ManchesterStingerMotorsports/BSPD-2026/BSPD 1003/BSPD PCB/BSPD 1003.kicad_sch

## KiCad design BSPD 1003/BSPD PCB/BSPD 1003.kicad_sch (2026-02-10)

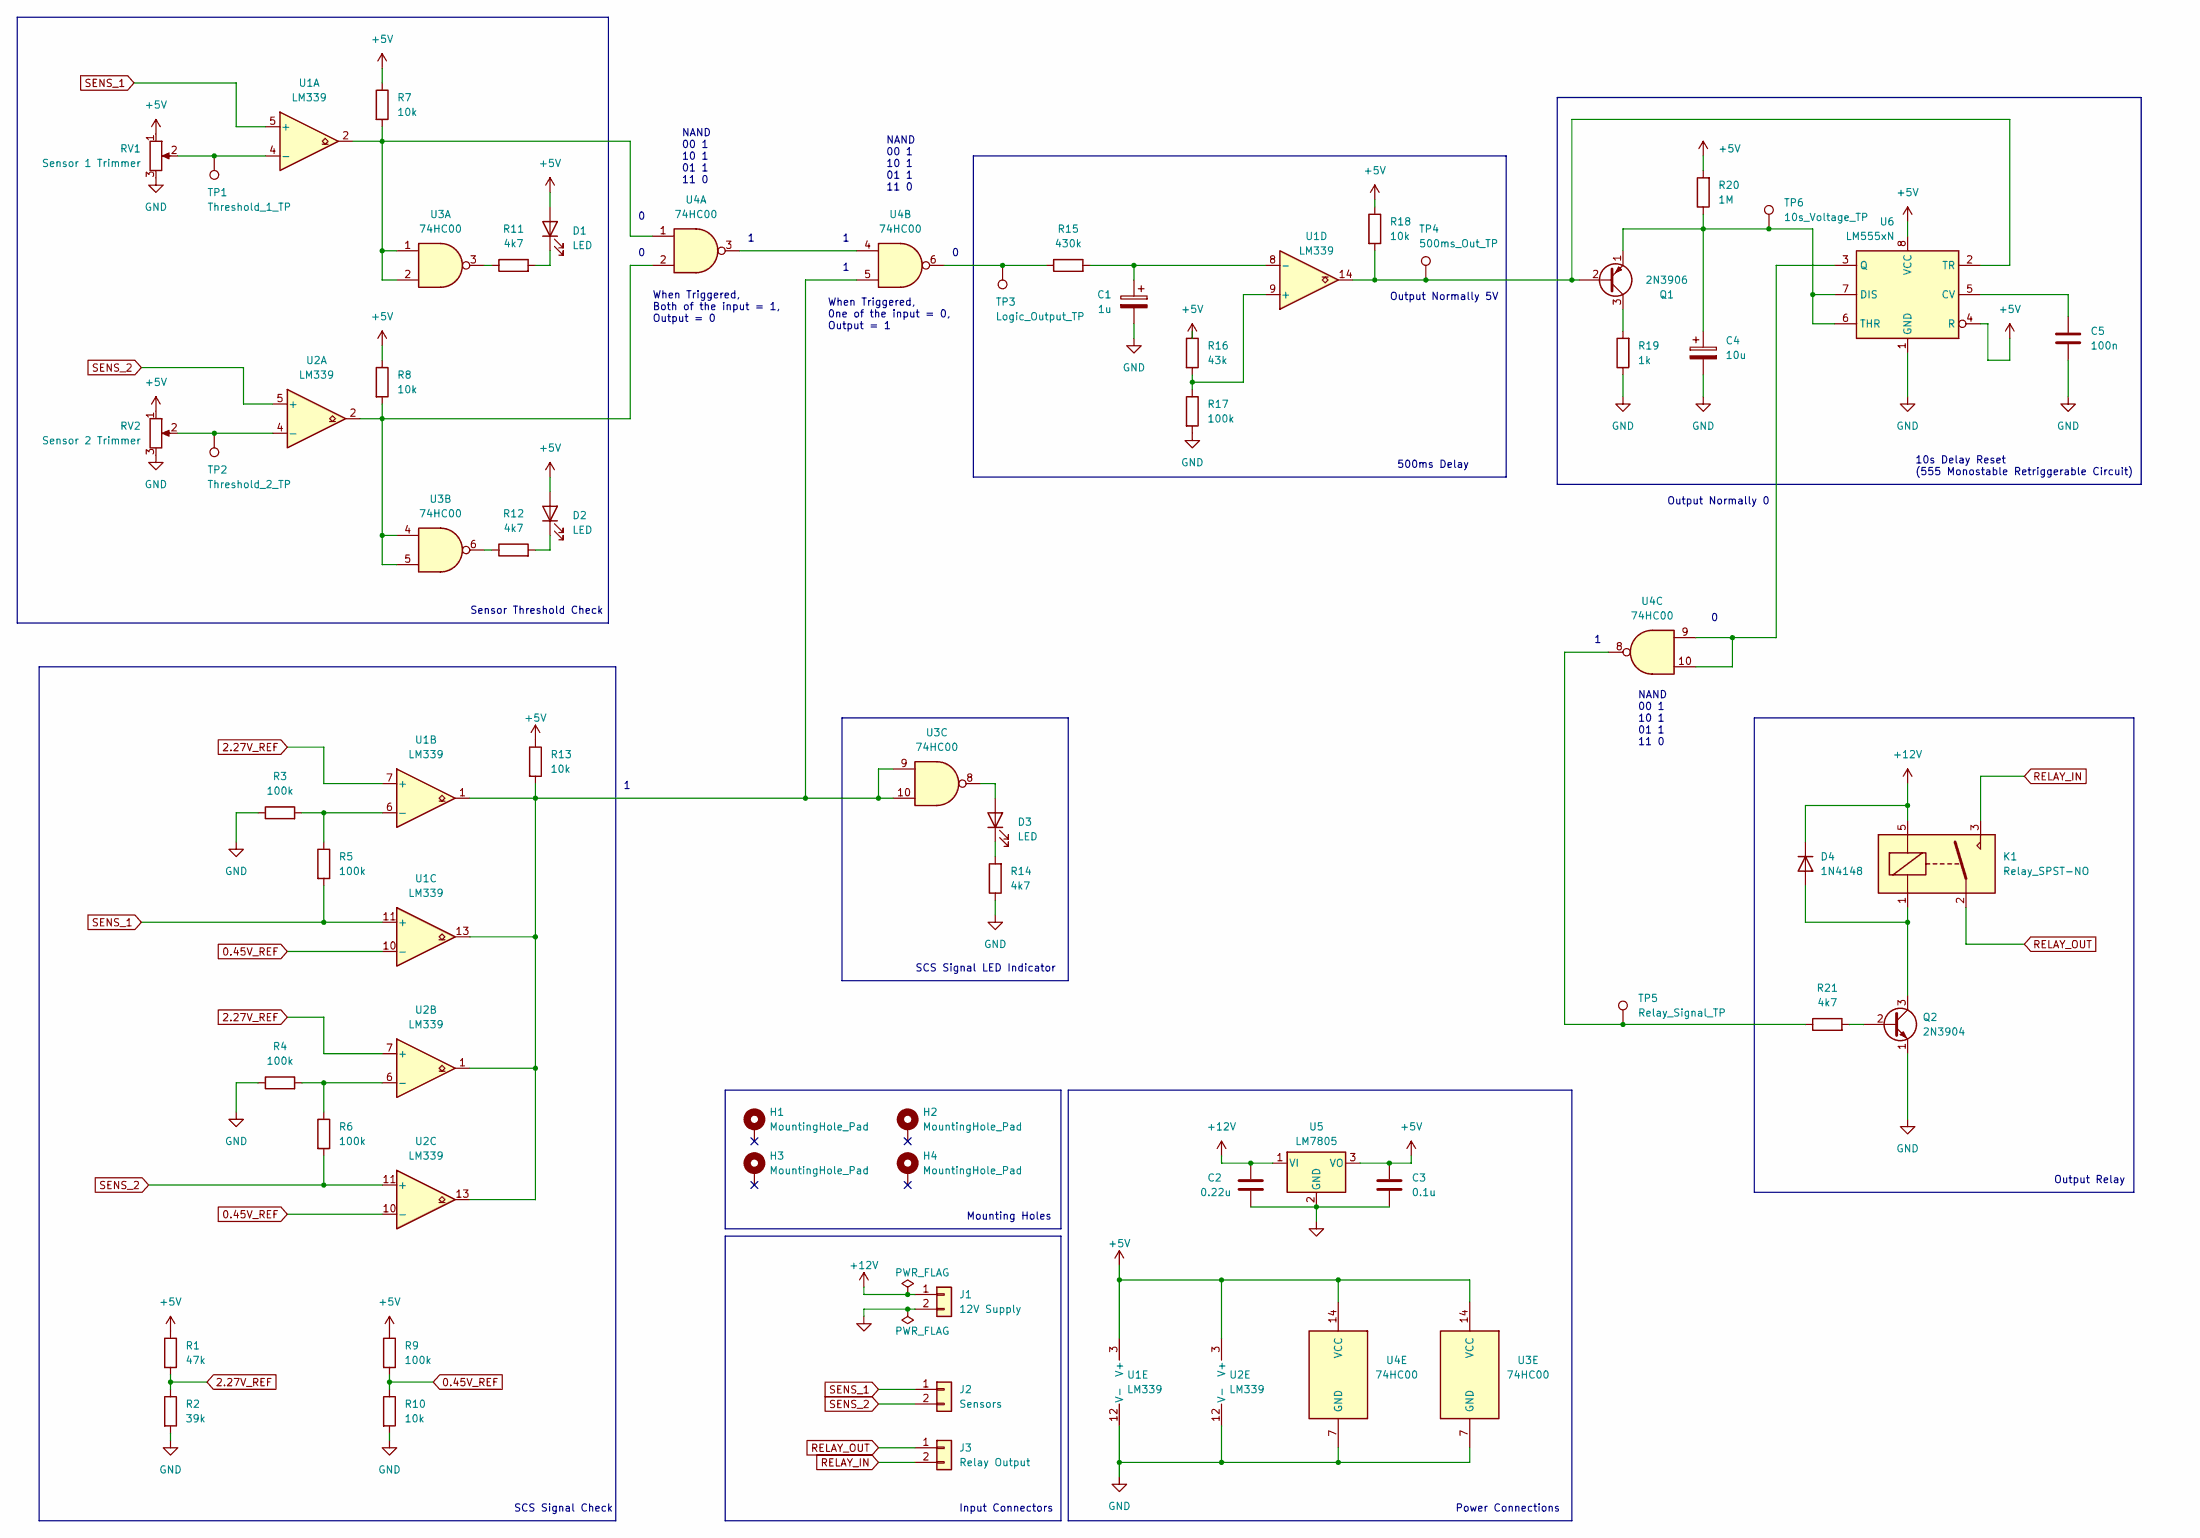
[picture p3: schematic BSPD 1003.kicad_sch]

Parts:
C1: 1u; CP_Radial_D5.0mm_P2.00mm
C2: 0.22u; C_Disc_D8.0mm_W2.5mm_P5.00mm
C3: 0.1u; C_Disc_D8.0mm_W2.5mm_P5.00mm
C4: 10u; CP_Radial_D5.0mm_P2.00mm
C5: 100n; C_Disc_D8.0mm_W2.5mm_P5.00mm
D1, D2, D3: LED; LED_D3.0mm
D4: 1N4148; D_DO-35_SOD27_P7.62mm_Horizontal
H1, H2, H3, H4: MountingHole_Pad; MountingHole_3.2mm_M3_DIN965_Pad
J1: 12V Supply; JST_VH_B2P-VH-FB-B_1x02_P3.96mm_Vertical
J2: Sensors; TerminalBlock_Phoenix_MPT-0,5-2-2.54_1x02_P2.54mm_Horizontal
J3: Relay Output; JST_VH_B2P-VH-FB-B_1x02_P3.96mm_Vertical
K1: Relay_SPST-NO; ALQ305
Q1: 2N3906; TO-92L_Wide
Q2: 2N3904; TO-92L_Wide
R1: 47k; R_Axial_DIN0207_L6.3mm_D2.5mm_P10.16mm_Horizontal
R2: 39k; R_Axial_DIN0207_L6.3mm_D2.5mm_P10.16mm_Horizontal
R3, R4, R5, R6, R9, R17: 100k; R_Axial_DIN0207_L6.3mm_D2.5mm_P10.16mm_Horizontal
R7, R8, R10, R13, R18: 10k; R_Axial_DIN0207_L6.3mm_D2.5mm_P10.16mm_Horizontal
R11, R12, R14, R21: 4k7; R_Axial_DIN0207_L6.3mm_D2.5mm_P10.16mm_Horizontal
R15: 430k; R_Axial_DIN0207_L6.3mm_D2.5mm_P10.16mm_Horizontal
R16: 43k; R_Axial_DIN0207_L6.3mm_D2.5mm_P10.16mm_Horizontal
R19: 1k; R_Axial_DIN0207_L6.3mm_D2.5mm_P10.16mm_Horizontal
R20: 1M; R_Axial_DIN0207_L6.3mm_D2.5mm_P10.16mm_Horizontal
RV1: Sensor 1 Trimmer; Potentiometer_Bourns_3386P_Vertical
RV2: Sensor 2 Trimmer; Potentiometer_Bourns_3386P_Vertical
TP1: Threshold_1_TP; TestPoint_Loop_D1.80mm_Drill1.0mm_Beaded
TP2: Threshold_2_TP; TestPoint_Loop_D1.80mm_Drill1.0mm_Beaded
TP3: Logic_Output_TP; TestPoint_Loop_D1.80mm_Drill1.0mm_Beaded
TP4: 500ms_Out_TP; TestPoint_Loop_D1.80mm_Drill1.0mm_Beaded
TP5: Relay_Signal_TP; TestPoint_Loop_D1.80mm_Drill1.0mm_Beaded
TP6: 10s_Voltage_TP; TestPoint_Loop_D1.80mm_Drill1.0mm_Beaded
U1, U2: LM339; DIP-14_W7.62mm
U3, U4: 74HC00; DIP-14_W7.62mm
U5: LM7805; TO-220-3_Horizontal_TabDown
U6: LM555xN; DIP-8_W7.62mm

Connections:
0.45V_REF: R9.2, R10.1, U1.10 (-), U2.10 (-)
2.27V_REF: R1.2, R2.1, U1.7 (+), U2.7 (+)
+5V: C3.1, D1.2 (A), D2.2 (A), R1.1, R7.1, R8.1, R9.1, R13.1, R16.1, R18.1, R20.2, RV1.1, RV2.1, U1.3 (V+), U2.3 (V+), U3.14 (VCC), U4.14 (VCC), U5.3 (VO), U6.4 (R), U6.8 (VCC)
+12V: C2.1, D4.1 (K), J1.1, K1.5, U5.1 (VI)
GND: C1.2, C2.2, C3.2, C4.2, C5.2, J1.2, Q2.1 (E), R2.2, R3.1, R4.1, R10.2, R14.1, R17.2, R19.1, RV1.3, RV2.3, U1.12 (V-), U2.12 (V-), U3.7 (GND), U4.7 (GND), U5.2 (GND), U6.1 (GND)
unnamed: C1.1, R15.2, U1.8 (-)
unnamed: C4.1, Q1.1 (E), R20.1, TP6.1, U6.6 (THR), U6.7 (DIS)
unnamed: C5.1, U6.5 (CV)
unnamed: D1.1 (K), R11.2
unnamed: D2.1 (K), R12.2
unnamed: D3.1 (K), R14.2
unnamed: D3.2 (A), U3.8
unnamed: D4.2 (A), K1.1, Q2.3 (C)
unnamed: Q1.2 (B), R18.2, TP4.1, U1.14, U6.2 (TR)
unnamed: Q1.3 (C), R19.2
unnamed: Q2.2 (B), R21.2
unnamed: R3.2, R5.1, U1.6 (-)
unnamed: R4.2, R6.1, U2.6 (-)
unnamed: R7.2, U1.2, U3.1, U3.2, U4.1
unnamed: R8.2, U2.2, U3.4, U3.5, U4.2
unnamed: R11.1, U3.3
unnamed: R12.1, U3.6
unnamed: R13.2, U1.1, U1.13, U2.1, U2.13, U3.9, U3.10, U4.5
unnamed: R15.1, TP3.1, U4.6
unnamed: R16.2, R17.1, U1.9 (+)
unnamed: R21.1, TP5.1, U4.8
unnamed: RV1.2, TP1.1, U1.4 (-)
unnamed: RV2.2, TP2.1, U2.4 (-)
unnamed: U4.3, U4.4
unnamed: U4.9, U4.10, U6.3 (Q)
RELAY_IN: J3.2, K1.3
RELAY_OUT: J3.1, K1.2
SENS_1: J2.1, R5.2, U1.5 (+), U1.11 (+)
SENS_2: J2.2, R6.2, U2.5 (+), U2.11 (+)

Notes on the sheet:
SCS Signal Check
When Triggered, Both of the input = 1, Output = 0
500ms Delay
Mounting Holes
Output Relay
SCS Signal LED Indicator
Power Connections
NAND 00 1 10 1 01 1 11 0
Sensor Threshold Check
Output Normally 5V
Input Connectors
When Triggered, 0ne of the input = 0, Output = 1
10s Delay Reset (555 Monostable Retriggerable Circuit)
Output Normally 0
